Rat-Rig/RatRig-PrintedParts/V-Core-3.0/PP000091-magnet_clip_V01_20230710.stl

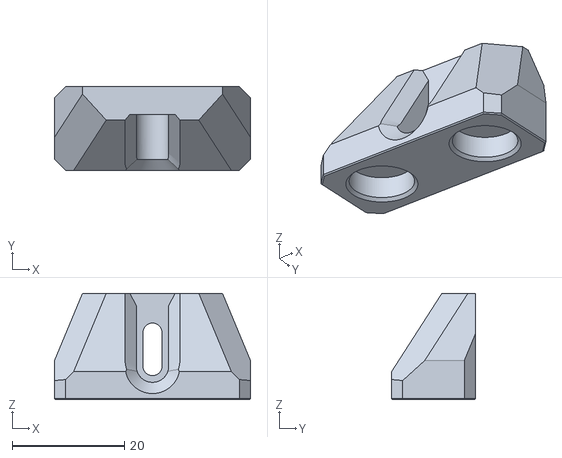
[picture p15: CAD file, 2023-07-10]
V-Core-3.0/PP000091-magnet_clip_V01_20230710.stl
35.0 x 15.0 x 19.0
