Rat-Rig/RatRig-PrintedParts/V-Core-3.1/PP000287-shelf_support_3.1_V01_20240116.stl

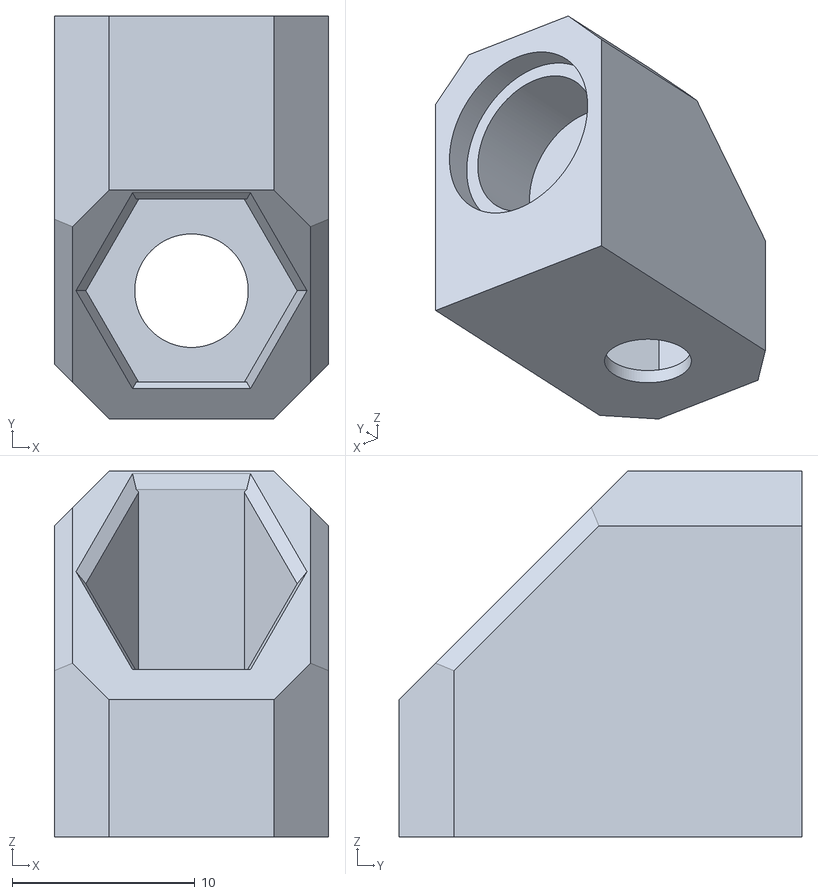
[picture p16: CAD file, 2024-01-16]
V-Core-3.1/PP000287-shelf_support_3.1_V01_20240116.stl
15.0 x 22.0 x 20.0
