Rat-Rig/RatRig-PrintedParts/V-Core-3.2H/PP000344-vc32h_tensioner_body_right_V01_20250702.stl

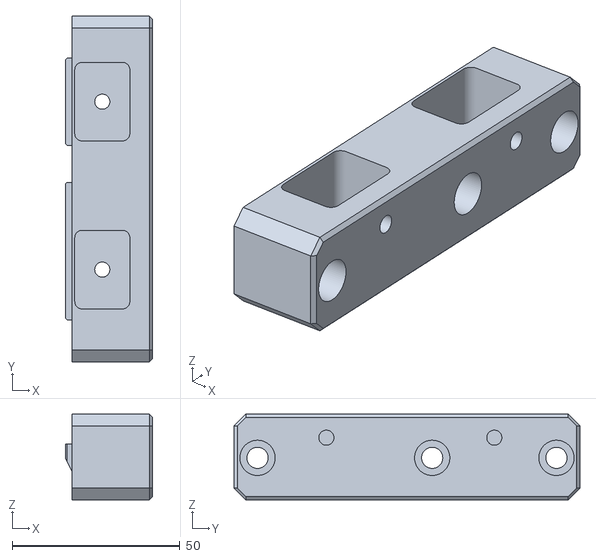
[picture p17: CAD file, 2025-07-31]
V-Core-3.2H/PP000344-vc32h_tensioner_body_right_V01_20250702.stl
26.0 x 103.0 x 25.5
