Rat-Rig/RatRig-PrintedParts/V-Core-4.0/PP000393-vc4_x-endstop_guard_V01_20250716.stl

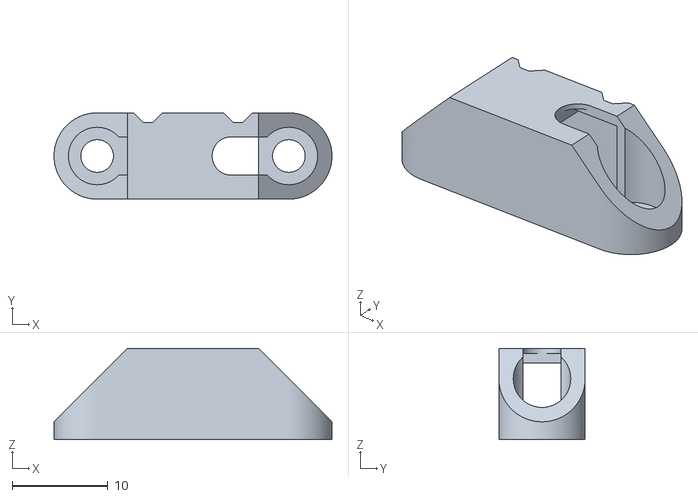
[picture p18: CAD file, 2025-07-17]
V-Core-4.0/PP000393-vc4_x-endstop_guard_V01_20250716.stl
29.0 x 9.00 x 9.50
